GenericLab/peepsy/GAPS-ElectricWonderland_2022/Lavayard-peepsy/WineyardPeepsy-MASK.png

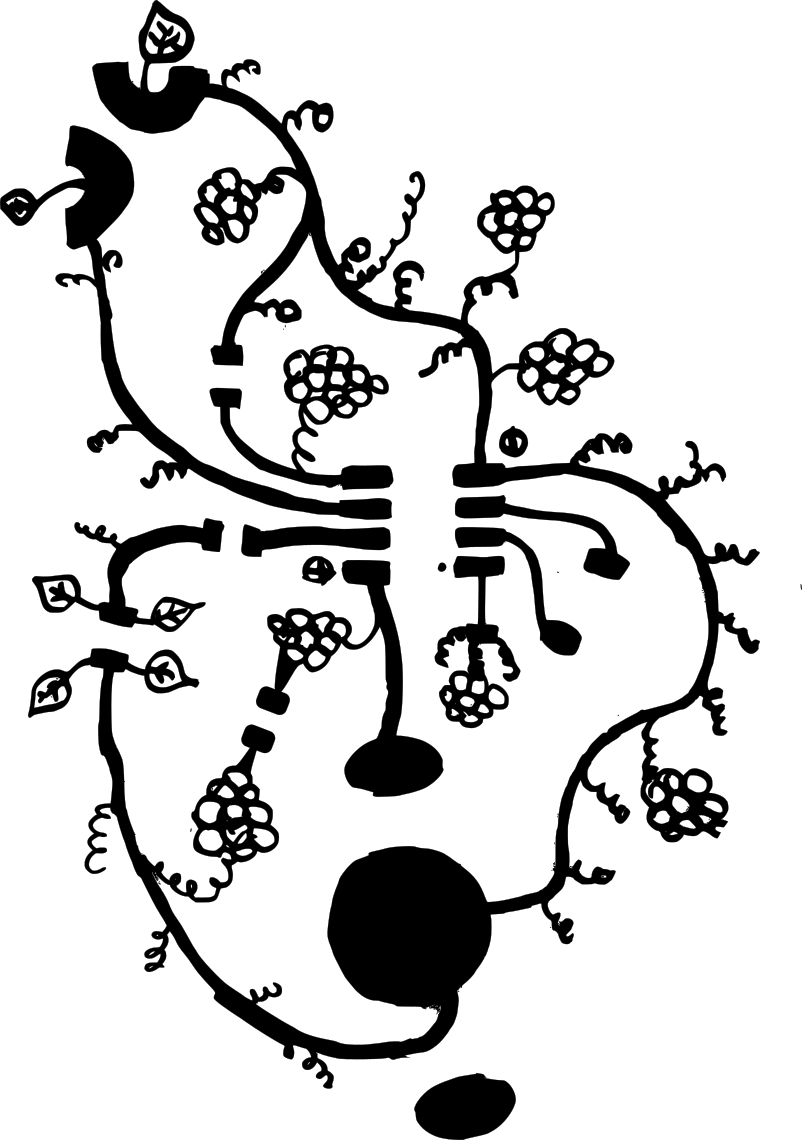
GAPS-ElectricWonderland_2022/Lavayard-peepsy/WineyardPeepsy-MASK.png
