GenericLab/peepsy/GAPS-ElectricWonderland_2022/Lavayard-peepsy/WineyardPeepsy_layout.png

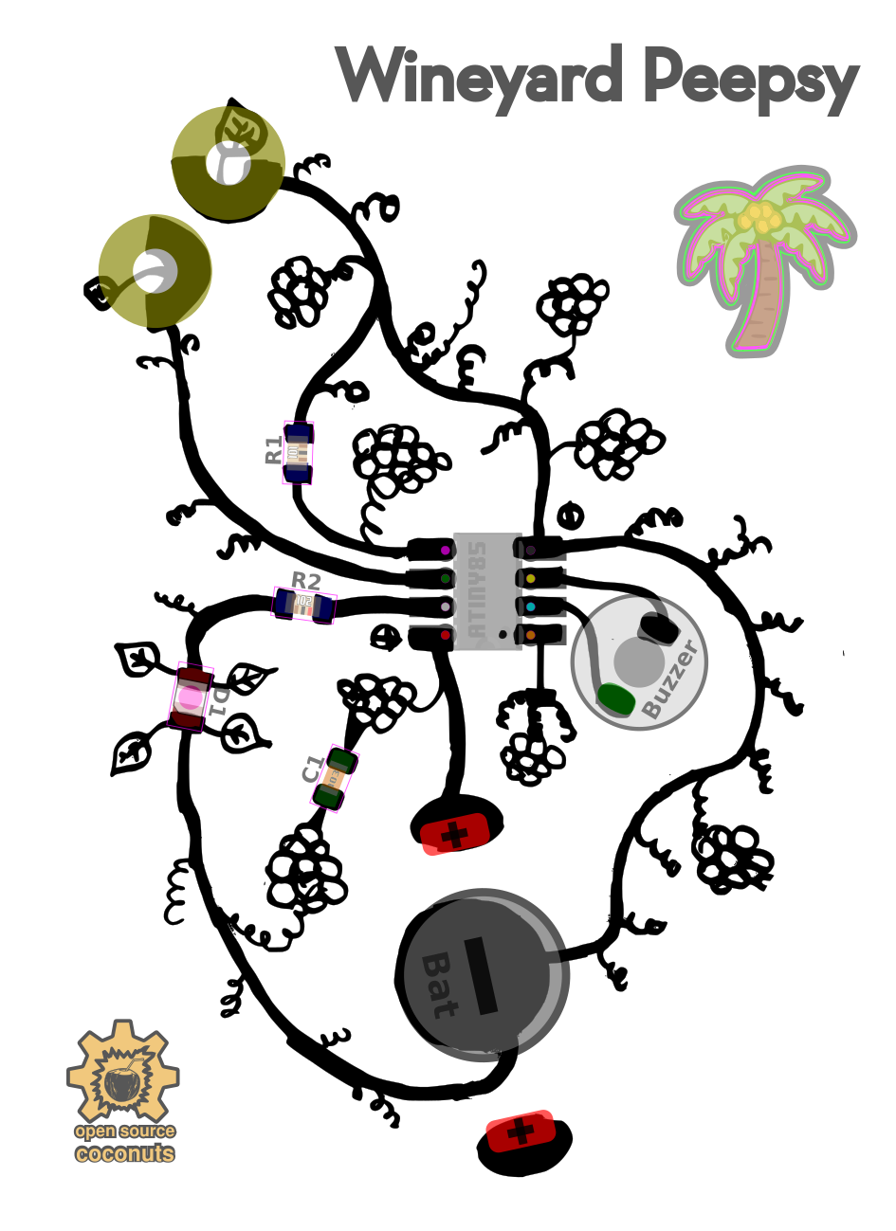
GAPS-ElectricWonderland_2022/Lavayard-peepsy/WineyardPeepsy_layout.png
