GenericLab/peepsy/GAPS-ElectricWonderland_2022/PandaClaw_etching.jpg

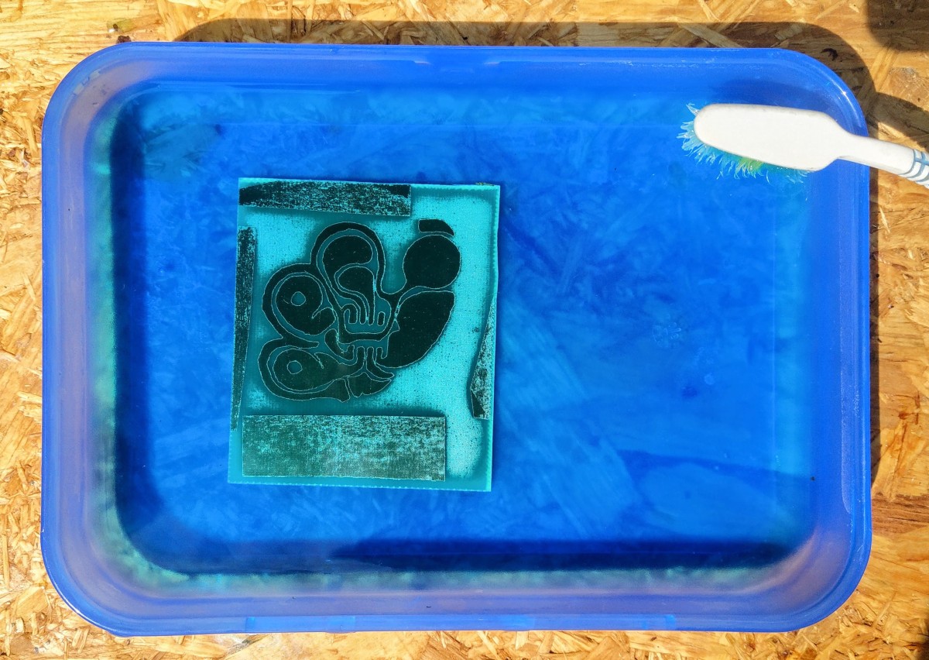
GAPS-ElectricWonderland_2022/PandaClaw_etching.jpg
