GenericLab/peepsy/GAPS-ElectricWonderland_2022/PandaClaw_PCB.jpg

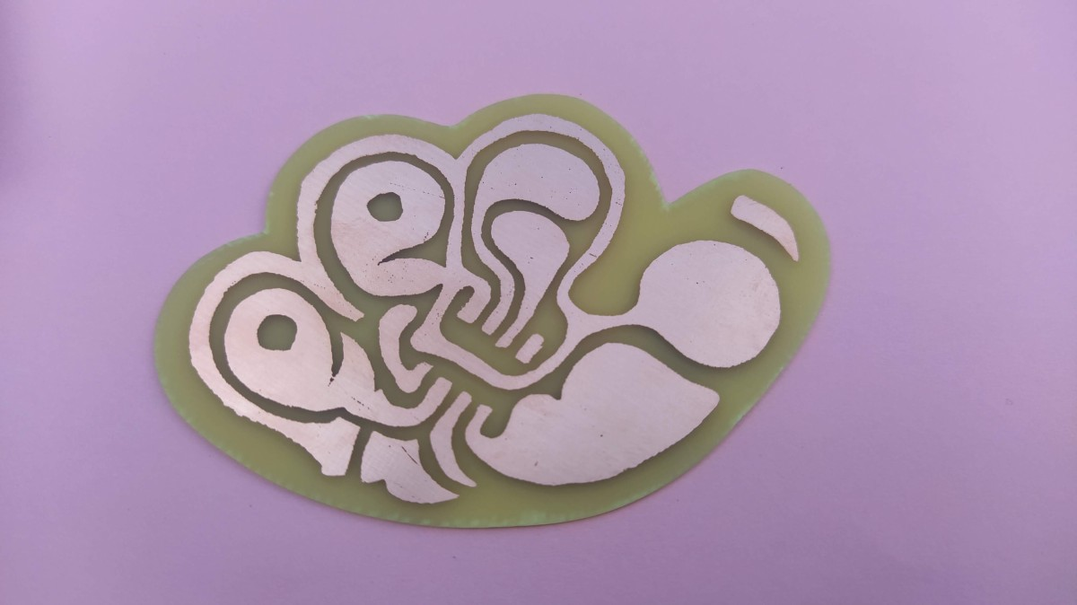
GAPS-ElectricWonderland_2022/PandaClaw_PCB.jpg
