GenericLab/peepsy/GAPS-ElectricWonderland_2022/PandaClaw_withBackground.jpg

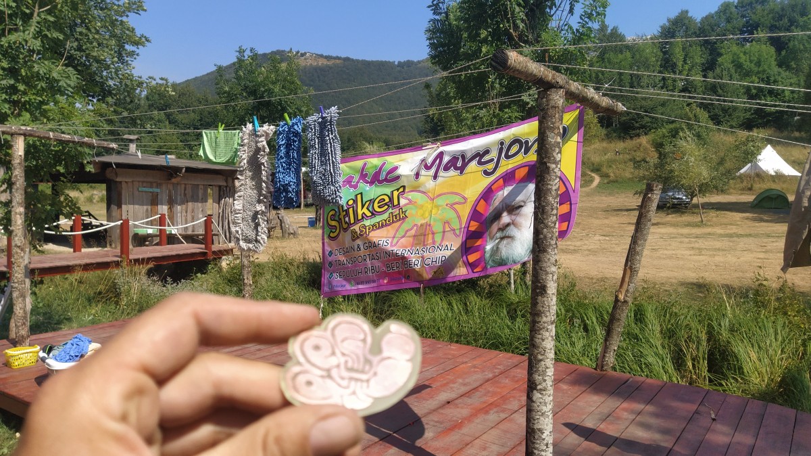
GAPS-ElectricWonderland_2022/PandaClaw_withBackground.jpg
