GenericLab/peepsy/GAPS-ElectricWonderland_2022/Wineyard_Drawing.jpg

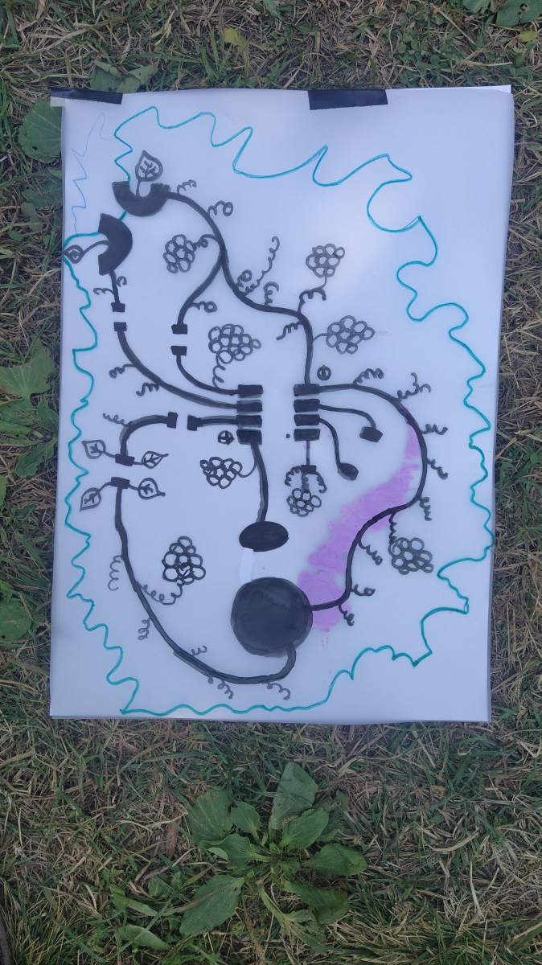
GAPS-ElectricWonderland_2022/Wineyard_Drawing.jpg
