GenericLab/peepsy/GAPS-ElectricWonderland_2022/Wineyard_pisibi.jpg

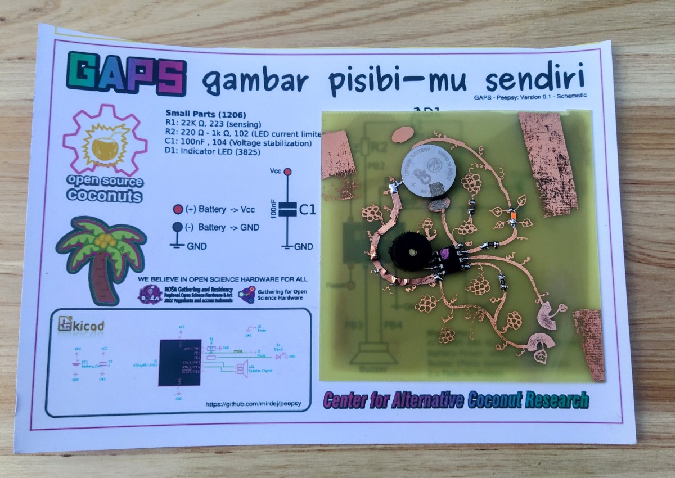
GAPS-ElectricWonderland_2022/Wineyard_pisibi.jpg
