GenericLab/peepsy/GAPS-Workshop_Yogya2022/PandaClaw/.svg2shenzhen-cache/images/B.Cu_g1204.png

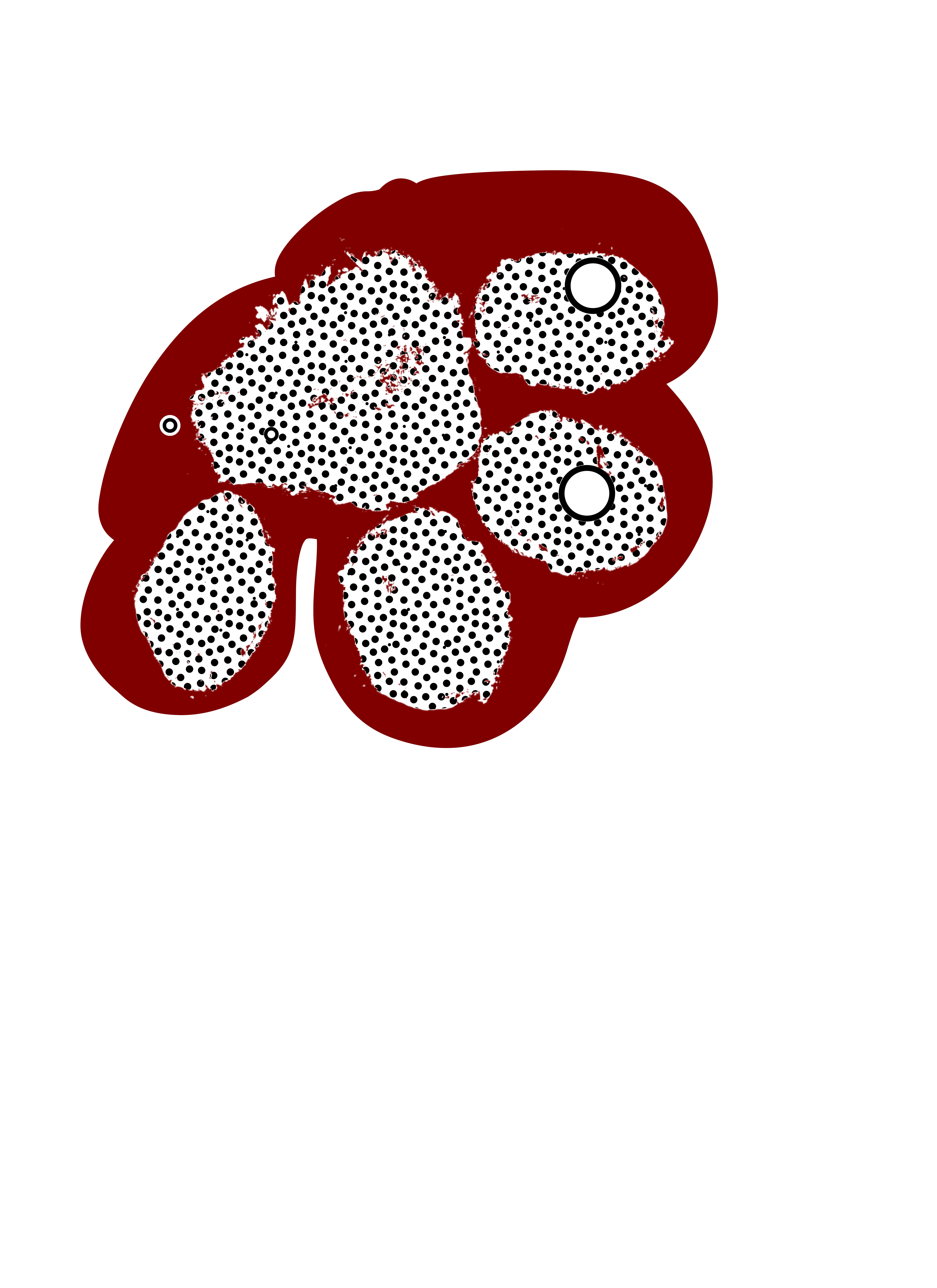
GAPS-Workshop_Yogya2022/PandaClaw/.svg2shenzhen-cache/images/B.Cu_g1204.png
