GenericLab/peepsy/GAPS-Workshop_Yogya2022/PandaClaw/.svg2shenzhen-cache/images/B.Mask_g1208.png

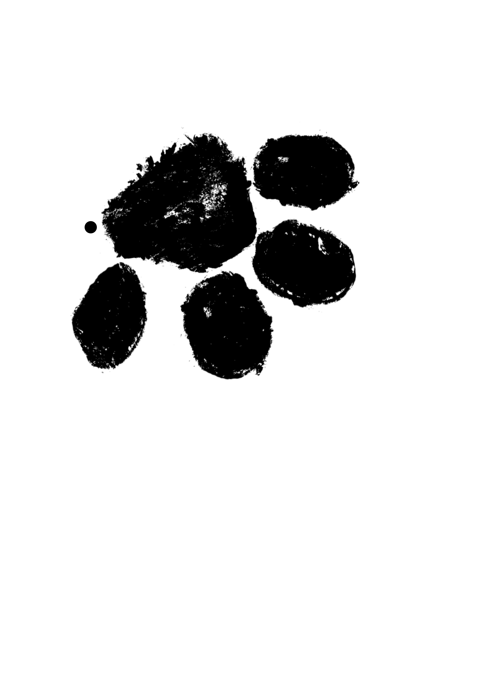
GAPS-Workshop_Yogya2022/PandaClaw/.svg2shenzhen-cache/images/B.Mask_g1208.png
