GenericLab/peepsy/GAPS-Workshop_Yogya2022/PandaClaw/.svg2shenzhen-cache/images/Dwgs.User_g1216.png

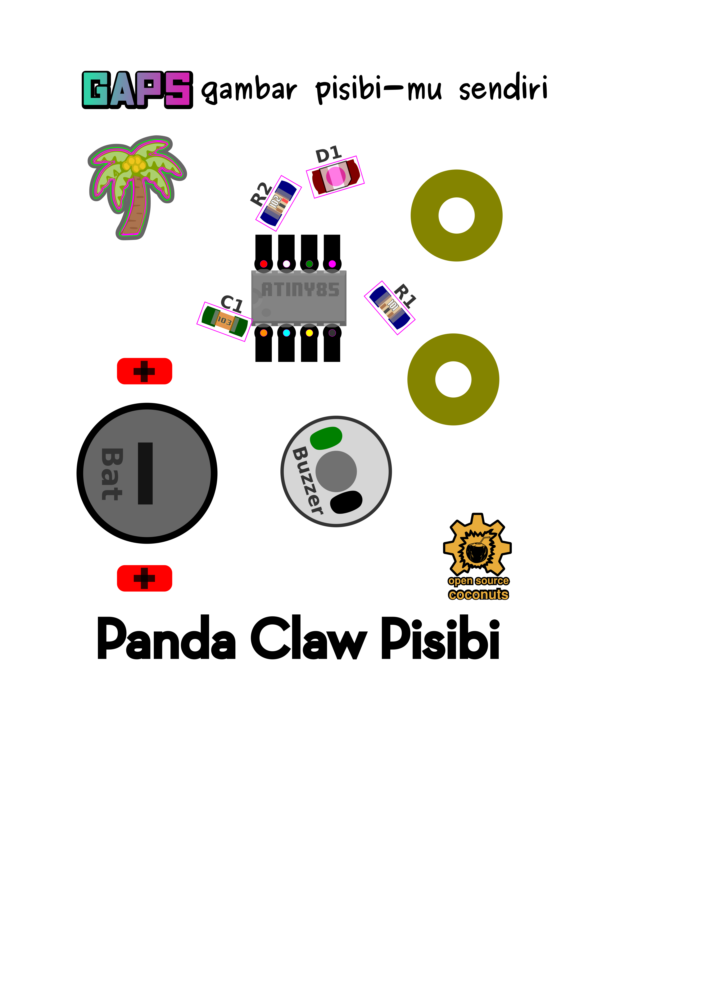
GAPS-Workshop_Yogya2022/PandaClaw/.svg2shenzhen-cache/images/Dwgs.User_g1216.png
