GenericLab/peepsy/GAPS-Workshop_Yogya2022/PandaClaw/.svg2shenzhen-cache/images/F.Cu_g1210.png

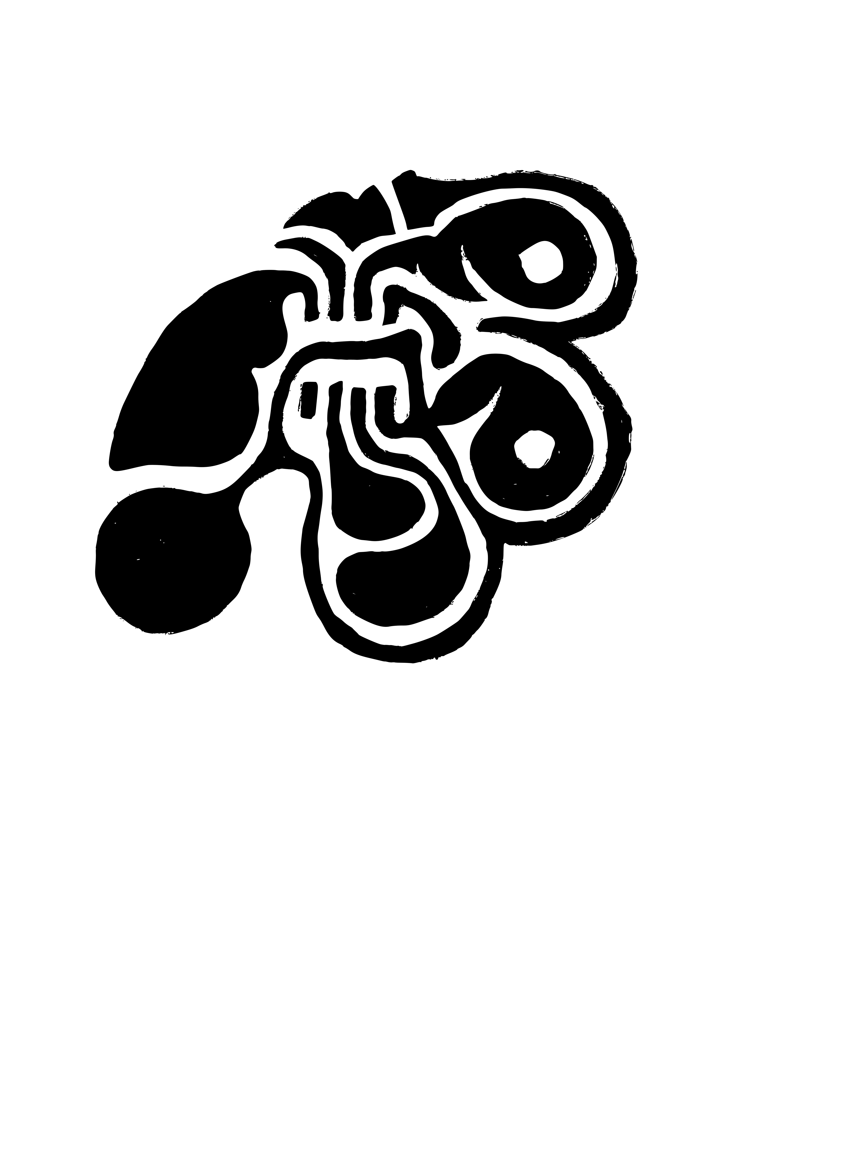
GAPS-Workshop_Yogya2022/PandaClaw/.svg2shenzhen-cache/images/F.Cu_g1210.png
