GenericLab/peepsy/GAPS-Workshop_Yogya2022/PandaClaw/.svg2shenzhen-cache/images/F.SilkS_g1214.png

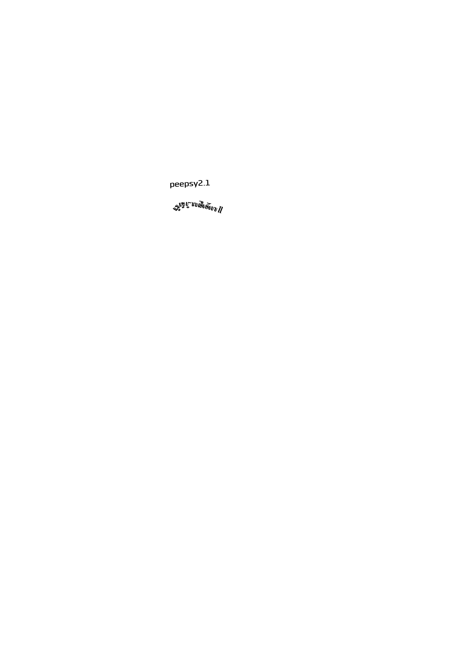
GAPS-Workshop_Yogya2022/PandaClaw/.svg2shenzhen-cache/images/F.SilkS_g1214.png
