GenericLab/peepsy/GAPS-Workshop_Yogya2022/PandaClaw/C9082E260E8566BF.png

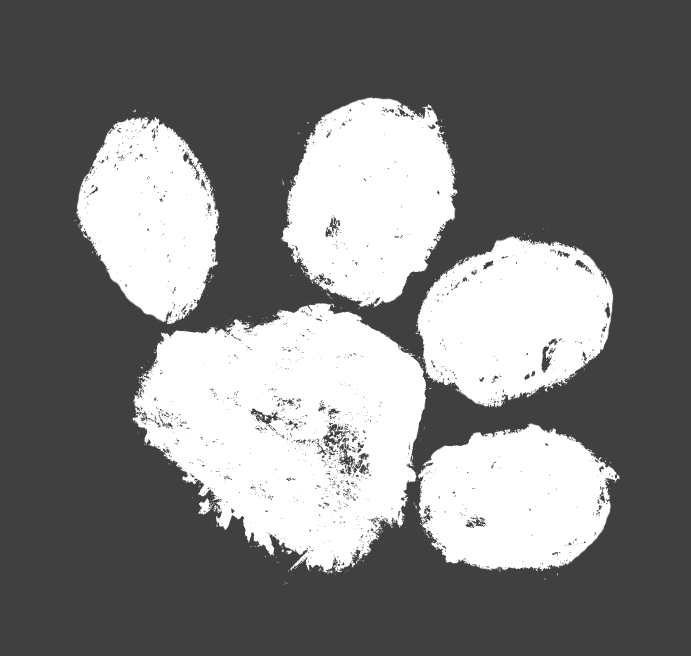
GAPS-Workshop_Yogya2022/PandaClaw/C9082E260E8566BF.png
