GenericLab/peepsy/GAPS-Workshop_Yogya2022/PandaClaw/Panda_footprint.png

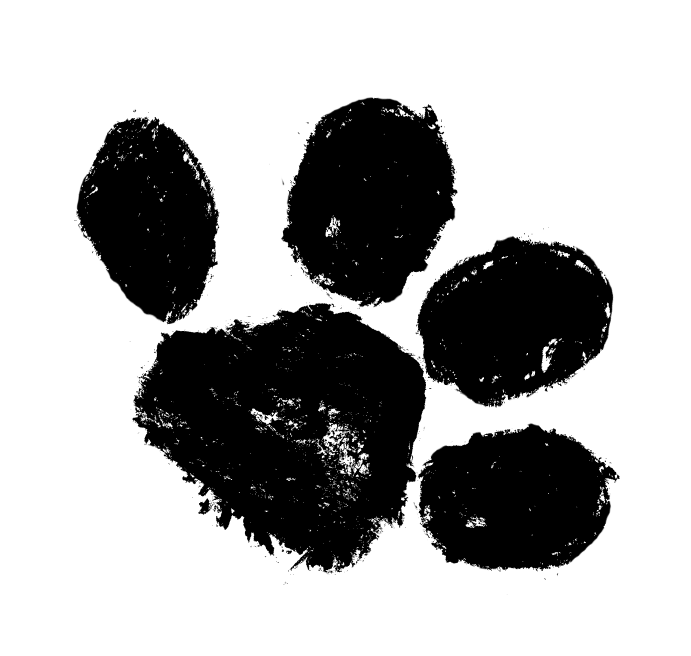
GAPS-Workshop_Yogya2022/PandaClaw/Panda_footprint.png
