GenericLab/peepsy/GAPS-Workshop_Yogya2022/PandaClaw/PandaCalwPeepsy_layout.png

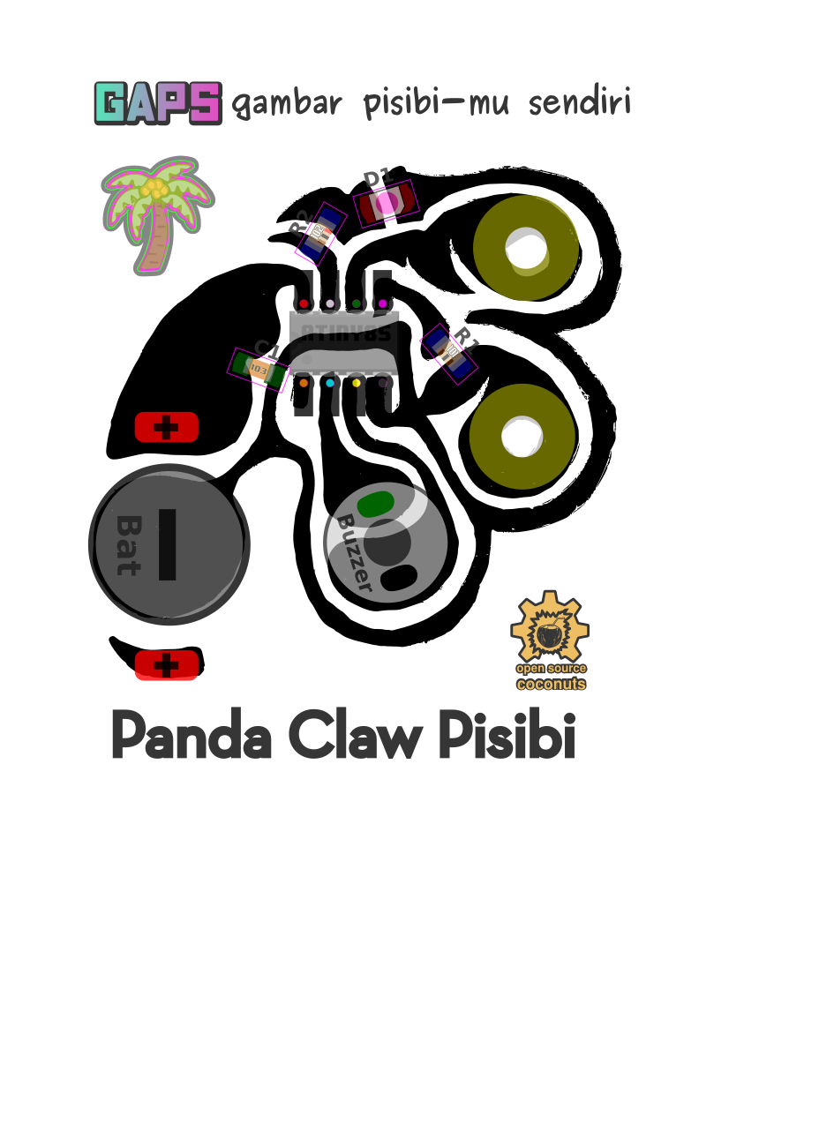
GAPS-Workshop_Yogya2022/PandaClaw/PandaCalwPeepsy_layout.png
