GenericLab/peepsy/GAPS-Workshop_Yogya2022/PandaClaw/PandaClawPeepsy-MASK.png

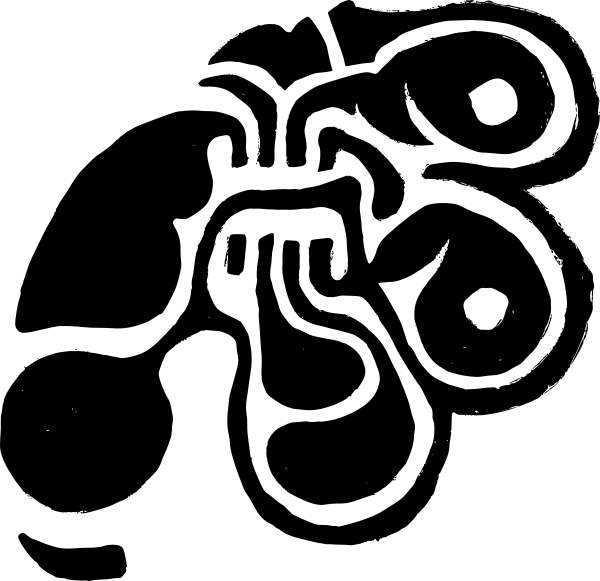
GAPS-Workshop_Yogya2022/PandaClaw/PandaClawPeepsy-MASK.png
