GenericLab/peepsy/GAPS_gudksul_sep2022/design_photos/IMG_20220926_174948.jpg

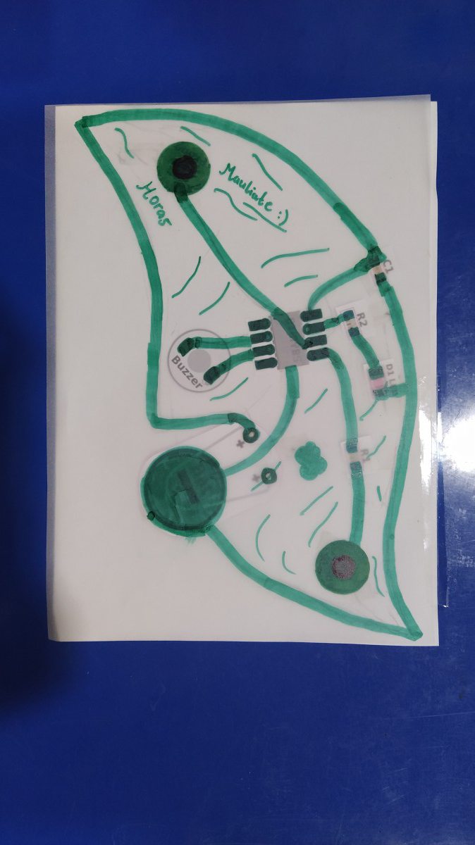
GAPS_gudksul_sep2022/design_photos/IMG_20220926_174948.jpg
