GenericLab/peepsy/GAPS_gudksul_sep2022/design_photos/IMG_20220926_175335.jpg

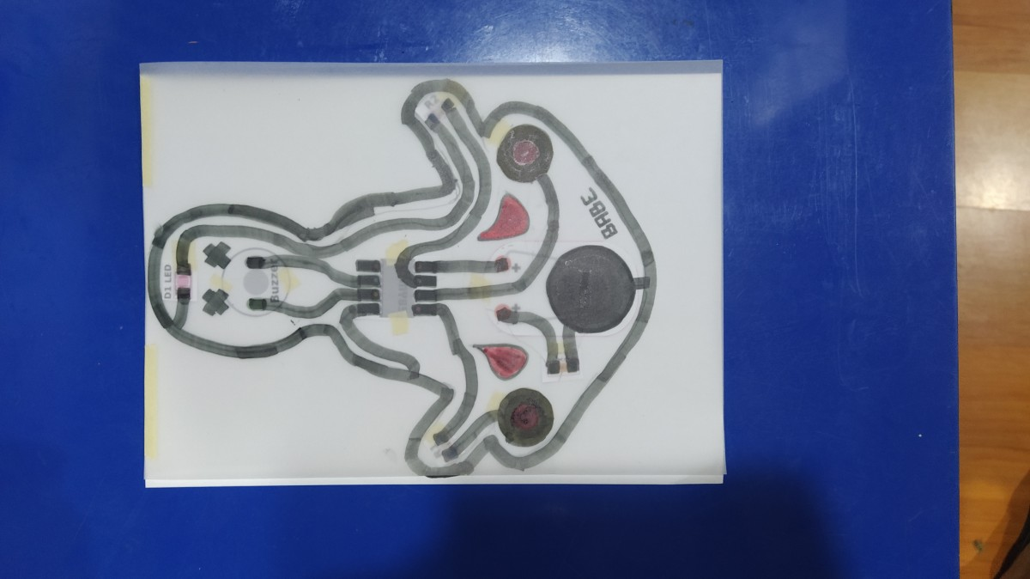
GAPS_gudksul_sep2022/design_photos/IMG_20220926_175335.jpg
