GenericLab/peepsy/GAPS_gudksul_sep2022/GAPS-Workshop_dusjagrMentoring.jpg

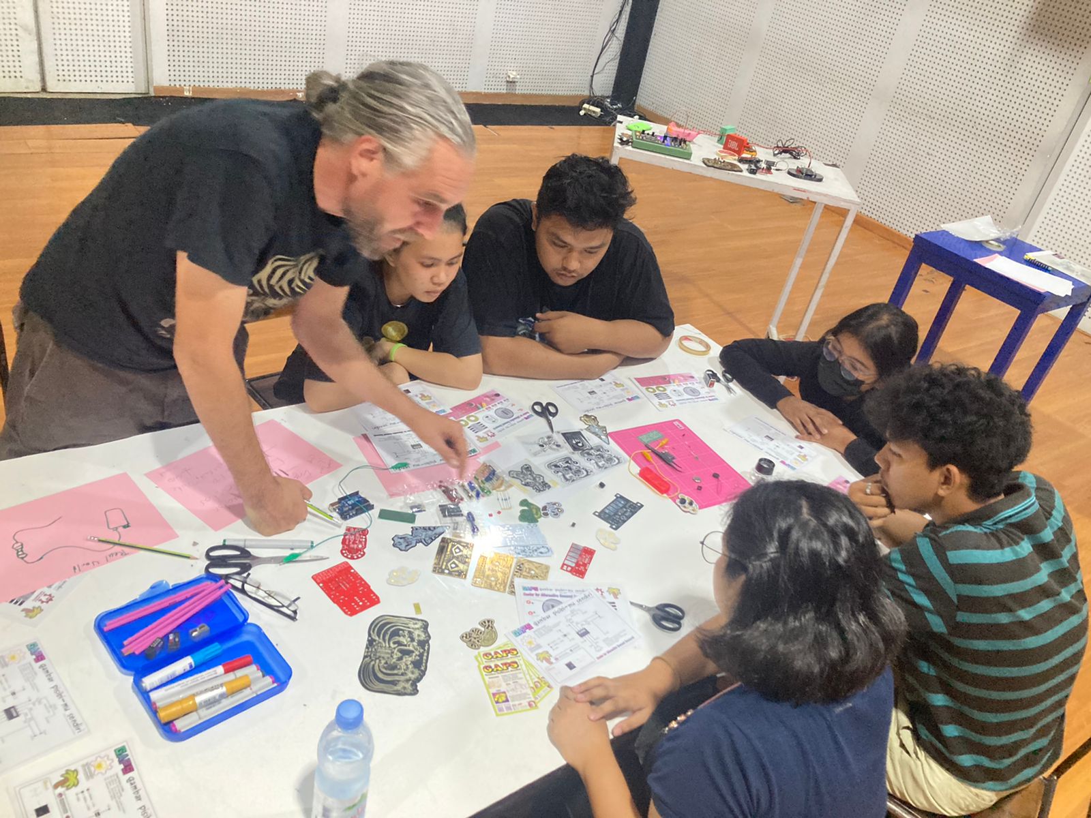
GAPS_gudksul_sep2022/GAPS-Workshop_dusjagrMentoring.jpg
