GenericLab/peepsy/laminates/GAPS_fiky_drawing.jpg

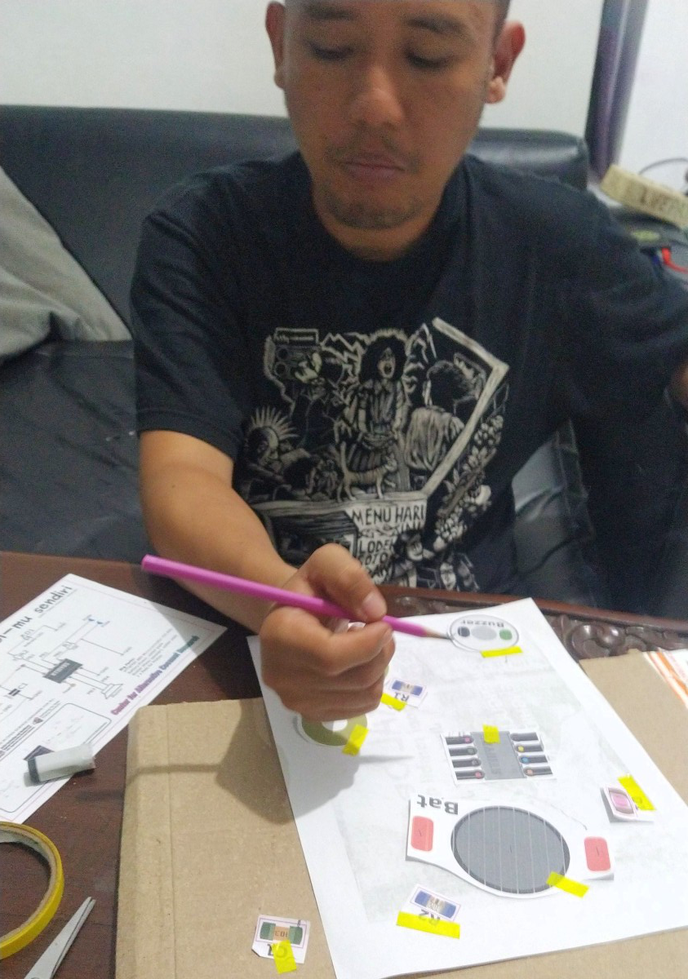
laminates/GAPS_fiky_drawing.jpg
